CrashTestCharlie/Qidi-X-Smart-3/configs/printer.cfg

#Mates3
#V4.1.11
# This file contains common pin mappings for QIDI
# boards. To use this config, the firmware should be compiled for the
# stm32f402. When running "make menuconfig", select the 48KiB
# bootloader, and enable "Serial for communication" and select the "on USART1 PA10/PA9"

# See docs/Config_Reference.md for a description of parameters.
[include x-smart-3/*.cfg]

# Calibrations
[extruder]
# auto-cal

[heater_bed]
# auto-cal

#*# <---------------------- SAVE_CONFIG ---------------------->
#*# DO NOT EDIT THIS BLOCK OR BELOW. The contents are auto-generated.
#*#
#*# [input_shaper]
#*# shaper_type_x = zv
#*# shaper_freq_x = 64.4
#*# shaper_type_y = mzv
#*# shaper_freq_y = 54.8
#*#
#*# [probe]
#*# z_offset = 0.000
#*#
#*# [bed_mesh default]
#*# version = 1
#*# points =
#*# 	-0.126250, -0.105000, -0.120000, -0.146250, -0.173750
#*# 	-0.088750, -0.077500, -0.072500, -0.086250, -0.120000
#*# 	-0.030000, -0.007500, -0.026250, -0.051250, -0.063750
#*# 	-0.048750, -0.048750, -0.068750, -0.095000, -0.092500
#*# 	-0.105000, -0.100000, -0.126250, -0.146250, -0.146250
#*# tension = 0.2
#*# min_x = 30.0
#*# algo = lagrange
#*# y_count = 5
#*# mesh_y_pps = 2
#*# min_y = 15.0
#*# x_count = 5
#*# max_y = 170.0
#*# mesh_x_pps = 2
#*# max_x = 170.0
#*#
#*# [bed_mesh kamp]
#*# version = 1
#*# points =
#*# 	-0.126250, -0.105000, -0.120000, -0.146250, -0.173750
#*# 	-0.088750, -0.077500, -0.072500, -0.086250, -0.120000
#*# 	-0.030000, -0.007500, -0.026250, -0.051250, -0.063750
#*# 	-0.048750, -0.048750, -0.068750, -0.095000, -0.092500
#*# 	-0.105000, -0.100000, -0.126250, -0.146250, -0.146250
#*# tension = 0.2
#*# min_x = 30.0
#*# algo = lagrange
#*# y_count = 5
#*# mesh_y_pps = 2
#*# min_y = 15.0
#*# x_count = 5
#*# max_y = 170.0
#*# mesh_x_pps = 2
#*# max_x = 170.0
#*#
#*# [extruder]
#*# control = pid
#*# pid_kp = 39.059
#*# pid_ki = 16.275
#*# pid_kd = 23.435
#*#
#*# [heater_bed]
#*# control = pid
#*# pid_kp = 64.070
#*# pid_ki = 1.124
#*# pid_kd = 913.001
