CrashTestCharlie/Qidi-X-Smart-3/configs/x-smart-3/02-toolhead.cfg

[mcu MKS_THR]
serial:/dev/serial/by-id/usb-Klipper_rp2040_25D94D1523865658-if00
