CrashTestCharlie/Qidi-X-Smart-3/configs/x-smart-3/search.cfg

[gcode_macro SEARCH_VARS]
description: Search the printer object, S={some word}
gcode:
    {% set search = params.S|lower %}
    {% set ns = namespace() %}
    {% for item in printer  %}
        {% if ' ' in item %}
            {% set ns.path = ['printer', "['%s']" % (item), ''] %}
        {% else %}
            {% set ns.path = ['printer.', item, ''] %}   
        {% endif %} 

        {% if search in ns.path|lower %}
            { action_respond_info(ns.path|join) }
        {% endif %} 

        {% if printer[item].items() %}
            {% for childkey, child in printer[item].items() recursive %}
                {% set ns.path = ns.path[:loop.depth|int + 1] %}

                {% if ' ' in childkey %}
                    {% set null = ns.path.append("['%s']" % (childkey)) %}
                {% else %}
                    {% set null = ns.path.append(".%s" % (childkey)) %}
                {% endif %} 

                {% if child is mapping  %}
                    { loop(child.items()) }
                {% else %}
                    {% if search in ns.path|lower %}
                        { action_respond_info("%s : %s" % (ns.path|join, child)) }   
                    {% endif %} 
                {% endif %} 
                
            {% endfor %}
        {% endif %} 
    {% endfor %}
